nikolastankovic03/System-for-automatic-detection-of-the-last-touch-in-a-basketball/Images/Desktop Aplication/логин_форма.png

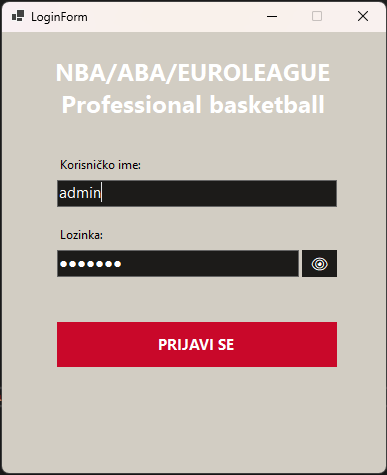
Images/Desktop Aplication/логин_форма.png
