nikolastankovic03/System-for-automatic-detection-of-the-last-touch-in-a-basketball/Images/PCB_Ball/3d_лопта_задња.png

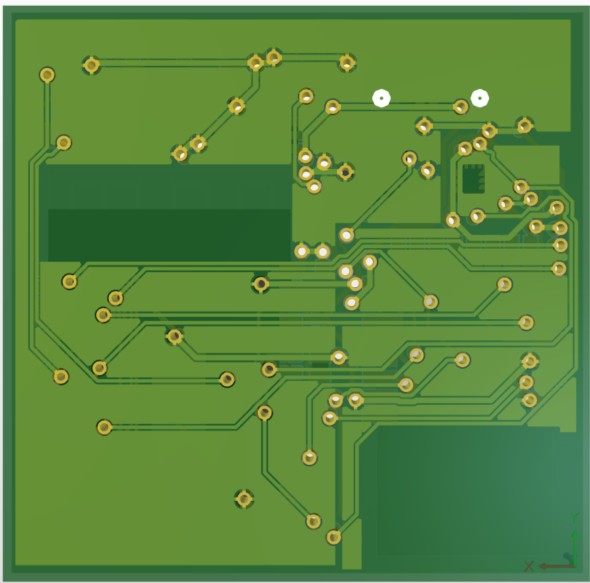
Images/PCB_Ball/3d_лопта_задња.png
