nikolastankovic03/System-for-automatic-detection-of-the-last-touch-in-a-basketball/Desktop application/Diplomski_Lopta/bin/Debug/net7.0-windows/aba.png

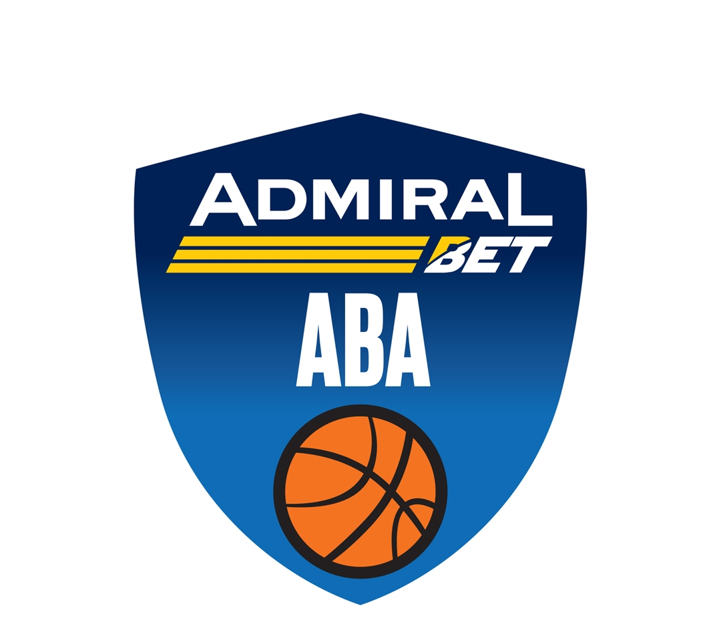
Desktop application/Diplomski_Lopta/bin/Debug/net7.0-windows/aba.png
